Supermagnum/double-gain/IMG_20210713_155857.jpg

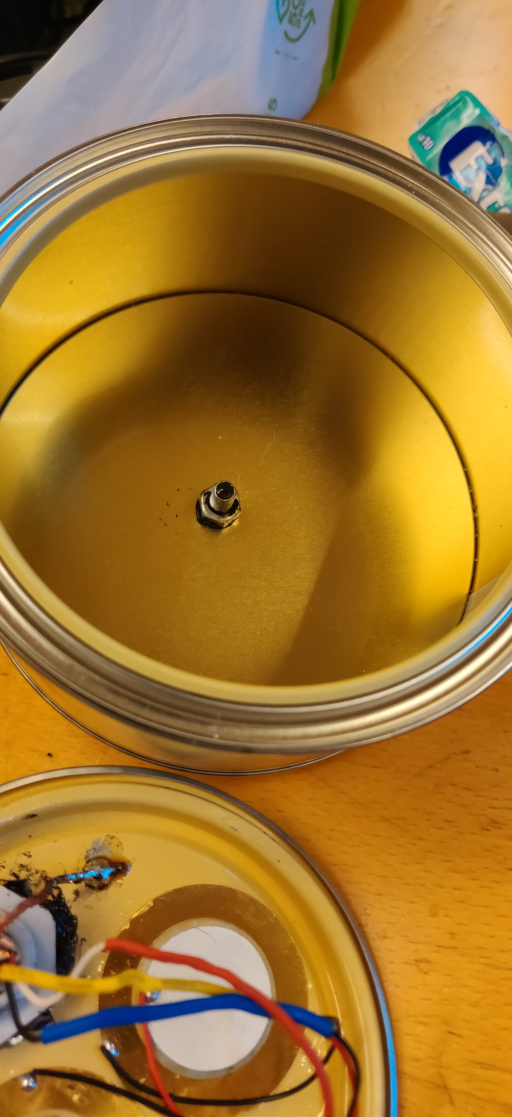
IMG_20210713_155857.jpg
