Supermagnum/double-gain/IMG_20210713_155905.jpg

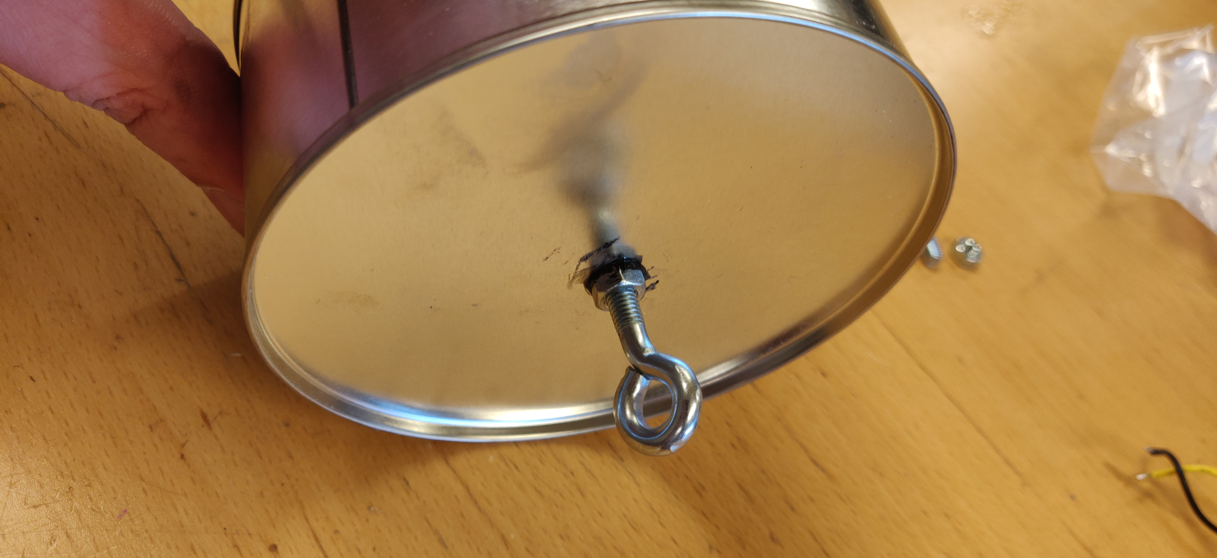
IMG_20210713_155905.jpg
