Supermagnum/double-gain/IMG_20210714_003702_205.jpg

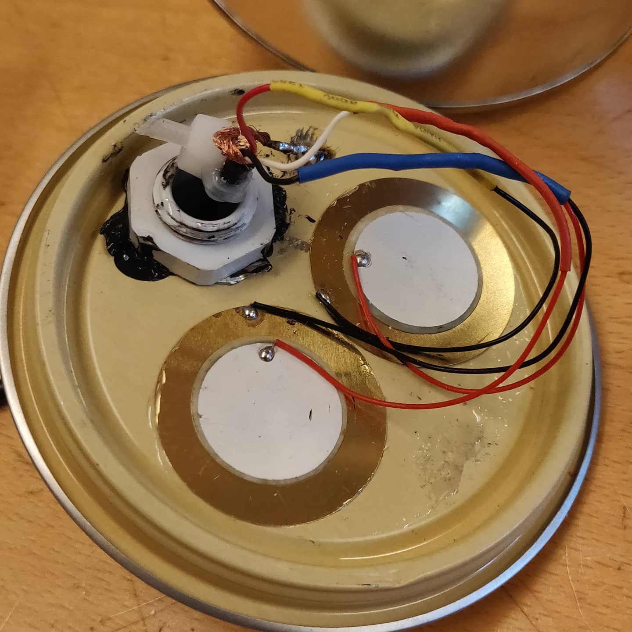
IMG_20210714_003702_205.jpg
