Supermagnum/double-gain/IMG_20210714_003702_212.jpg

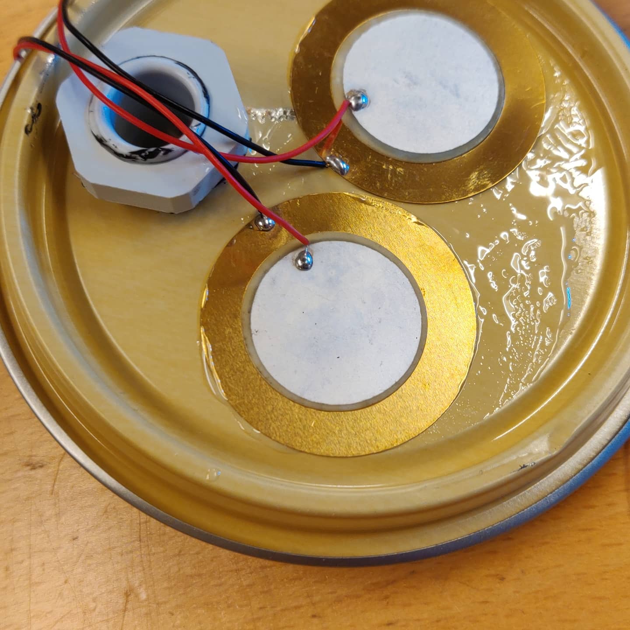
IMG_20210714_003702_212.jpg
