Supermagnum/double-gain/IMG_20210714_003702_220.jpg

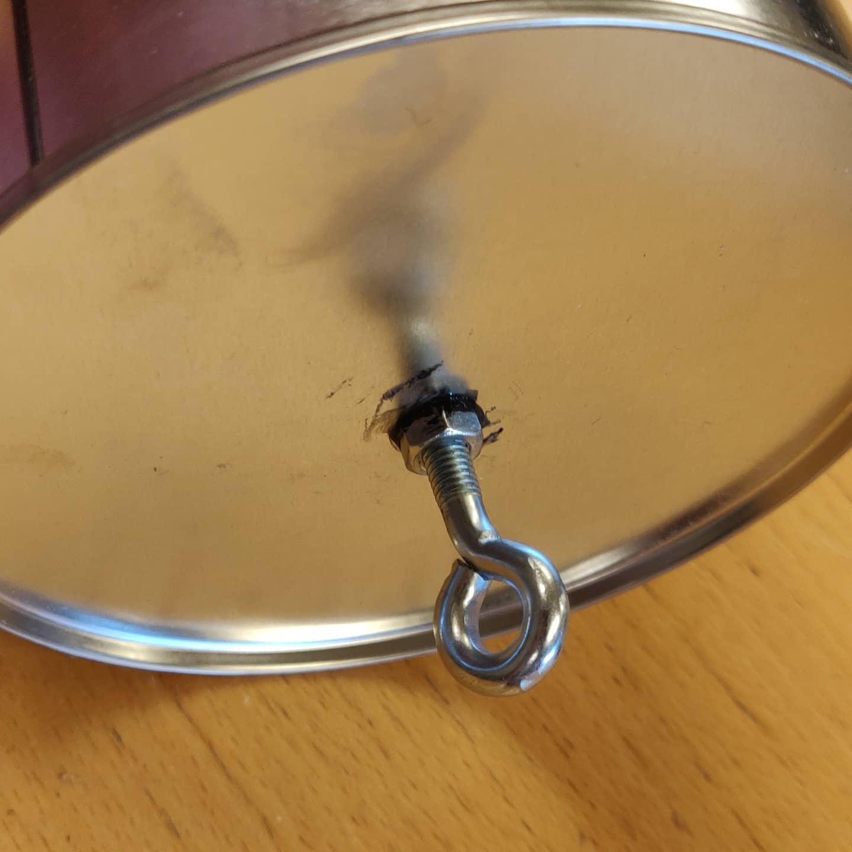
IMG_20210714_003702_220.jpg
