Supermagnum/double-gain/double-gain-balanced.asc

C1: cap; 10µF
C3: cap; 47µF
C4: cap; 47µF
C5: cap; 0.1µF
C6: cap; 47µF
C7: cap; 10µF
C8: cap; 47µF
C9: cap; 33µF
D1: zener; EDZV18B
R1: res; 1Meg; tol=1
R2: res; 56K; tol=1
R3: res; 56K; tol=1
R4: res; 1Meg; tol=1
R5: res; 9K; tol=1
R6: res; 100; tol=1
R7: res; 9K; tol=1
R8: res; 470; tol=1
R9: res; 10K; tol=1
R10: res; 100; tol=1
R11: res; 4.7K; tol=1
R12: res; 100; tol=1
R13: res; 470; tol=1
R14: res; 10K; tol=1
R15: res; 6.81K; tol=1
R16: res; 6.81K; tol=1
R17: res; 4.7K; tol=1
U1: NE5534
U2: NE5534
V1: voltage; 48
V2: voltage; SINE(0 0.1 1000); AC 0.1
V3: voltage; SINE(0 0.1 1000); AC 0.1
Named nets: 0, OUT+, OUT-
.tran 0 0.00000015 0 500
